leonvandenbeukel/Wi-Fi-Fish-Feeder-With-Camera/camera_index.h

//File: index_ov2640.html.gz, Size: 4316
#define index_ov2640_html_gz_len 4907
const uint8_t index_ov2640_html_gz[] = {
  0x1f,0x8b,0x08,0x08,0xf6,0x7c,0x55,0x5d,0x00,0xff,0x69,0x6e,0x64,0x65,0x78,0x5f,0x6f,0x76,0x32,0x36,0x34,0x30,0x5f,0x68,0x74,0x6d,0x6c,0x5f,0x67,0x7a,0x5f,0x6c,0x65,0x6e,0x00,0xe5,0x5d,0xfd,0x73,0xda,0x46,0xfa,0xff,0xbd,0x7f,0x85,0xac,0xf6,0x62,0x32,0x35,0x60,0xb0,0xeb,0xa4,0x9c,0x4d,0xbe,0x89,0xe3,0x24,0x9d,0x69,0xd2,0x5e,0xdc,0x6b,0x3b,0xd3,0xb9,0x49,0x04,0x5a,0x40,0x57,0x21,0x71,0x92,0x30,0x76,0x33,0xf9,0xdf,0xef,0xb3,0x2f,0x5a,0xad,0xc4,0x6a,0x25,0x81,0x0d,0xfd,0xf6,0x60,0x06,0x84,0xb4,0xcf,0xb3,0xcf,0xfb,0x3e,0xfb,0xca,0xf9,0x81,0x1b,0x8e,0x93,0xbb,0x05,0xb1,0x66,0xc9,0xdc,0x1f,0x7e,0x71,0xce,0xbf,0x2c,0xbc,0xce,0x67,0xc4,0x71,0xf9,0x25,0xfb,0x39,0x27,0x89,0x63,0x8d,0x67,0x4e,0x14,0x93,0xe4,0xc2,0x5e,0x26,0x93,0xf6,0x53,0xbb,0xf8,0x38,0x70,0xe6,0xe4,0xc2,0xbe,0xf1,0xc8,0x6a,0x11,0x46,0x89,0x6d,0x8d,0xc3,0x20,0x21,0x01,0x8a,0xaf,0x3c,0x37,0x99,0x5d,0xb8,0xe4,0xc6,0x1b,0x93,0x36,0xfb,0x71,0xe4,0x05,0x5e,0xe2,0x39,0x7e,0x3b,0x1e,0x3b,0x3e,0xb9,0xe8,0xa9,0xb8,0x12,0x2f,0xf1,0xc9,0xf0,0xea,0xfa,0xc7,0x93,0xbe,0xf5,0xc3,0xcf,0xfd,0xd3,0xb3,0xe3,0xf3,0x2e,0xbf,0x97,0x95,0x89,0x93,0x3b,0xf5,0x37,0x7d,0x8d,0x42,0xf7,0xce,0xfa,0x94,0xbb,0x45,0x5f,0x13,0x10,0xd1,0x9e,0x38,0x73,0xcf,0xbf,0x1b,0x58,0xcf,0x23,0xd4,0x79,0xf4,0x86,0xf8,0x37,0x24,0xf1,0xc6,0xce,0x51,0xec,0x04,0x71,0x3b,0x26,0x91,0x37,0xf9,0xfb,0x1a,0xe0,0xc8,0x19,0xff,0x3e,0x8d,0xc2,0x65,0xe0,0x0e,0xac,0x2f,0x7b,0x4f,0xe9,0x7b,0xbd,0xd0,0x38,0xf4,0xc3,0x08,0xcf,0xaf,0x5e,0xd1,0xf7,0xfa,0x73,0x56,0x7b,0xec,0xfd,0x41,0x0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
 0xC0, 0xC7, 0x1A, 0x95, 0x0B, 0x62, 0x46, 0xB5, 0x88, 0x3E, 0x6C, 0xD8, 0xA7, 0x42, 0xCA, 0x61,
 0x9F, 0xD2, 0x00, 0xD2, 0xE8, 0xC8, 0xD9, 0x17, 0xE1, 0xA5, 0x4A, 0x98, 0x87, 0x19, 0xFB, 0xCC,
 0xD1, 0x55, 0xBD, 0x10, 0xBB, 0x68, 0x50, 0x84, 0x21, 0x94, 0x59, 0xAB, 0x06, 0x43, 0x97, 0x33,
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
};
